egguy/py_mqtt_buzzer/boot.py

# This file is executed on every boot (including wake-boot from deepsleep)
#import esp
#esp.osdebug(None)
#import webrepl
#webrepl.start()


"""
def do_connect():
    import network
    wlan = network.WLAN(network.STA_IF)
    wlan.active(True)
    if not wlan.isconnected():
        print('connecting to network...')
        wlan.connect('HADOPI Suveillance Van', 'MyDuckIsReallyGreat')
        while not wlan.isconnected():
            pass
    print('network config:', wlan.ifconfig())
    return wlan
"""
